dryet/Clap-pixel/Clap-pixel-firmware/Core/Inc/control.h

/*
 * control.h
 *
 *  Created on: Apr 30, 2025
 *      Author: Petr Opravil
 */

 #ifndef INC_CONTROL_H_
 #define INC_CONTROL_H_
 
 #include "main.h"
 
 void Control_Init();
 void Control_Loop();
 
 #endif /* INC_CONTROL_H_ */
